jraivio/IoT-Ralli-Vempain/Hardware/Pictures/_DSC5884.JPG

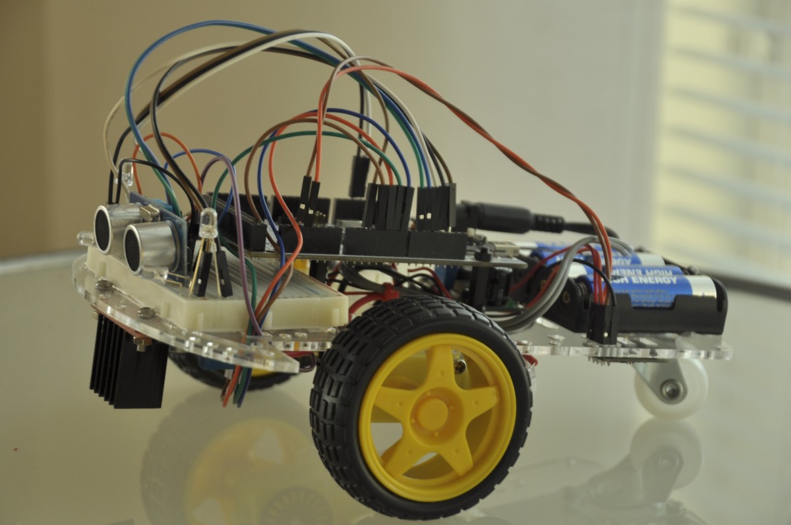
Hardware/Pictures/_DSC5884.JPG
