jraivio/IoT-Ralli-Vempain/Hardware/Pictures/Cloudyralli.png

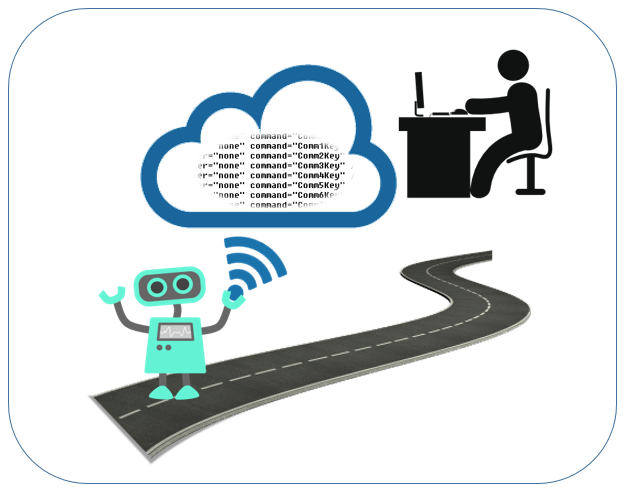
Hardware/Pictures/Cloudyralli.png
