jraivio/IoT-Ralli-Vempain/Hardware/Pictures/esp-link.png

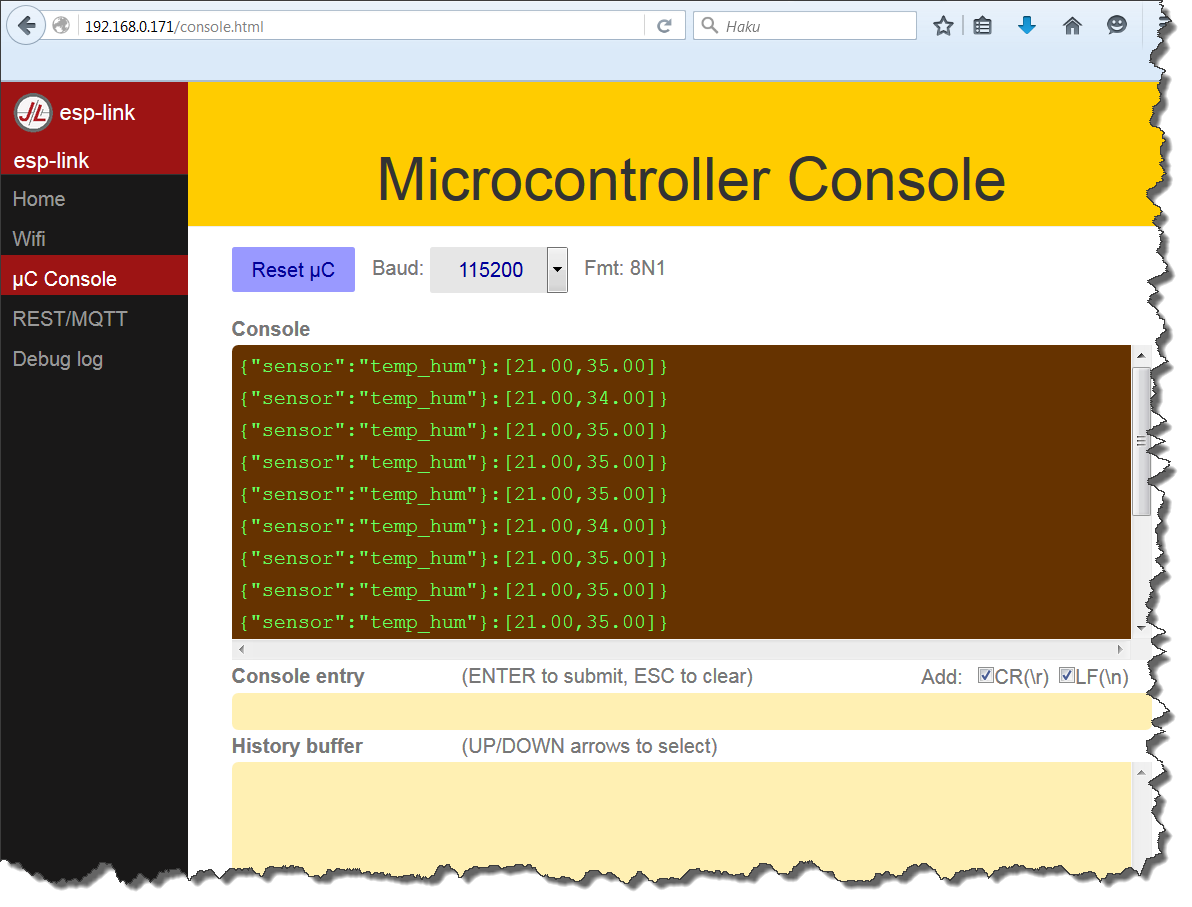
Hardware/Pictures/esp-link.png
