jraivio/IoT-Ralli-Vempain/Hardware/Pictures/Ralli-Vempain-Fritzing-wiring.png

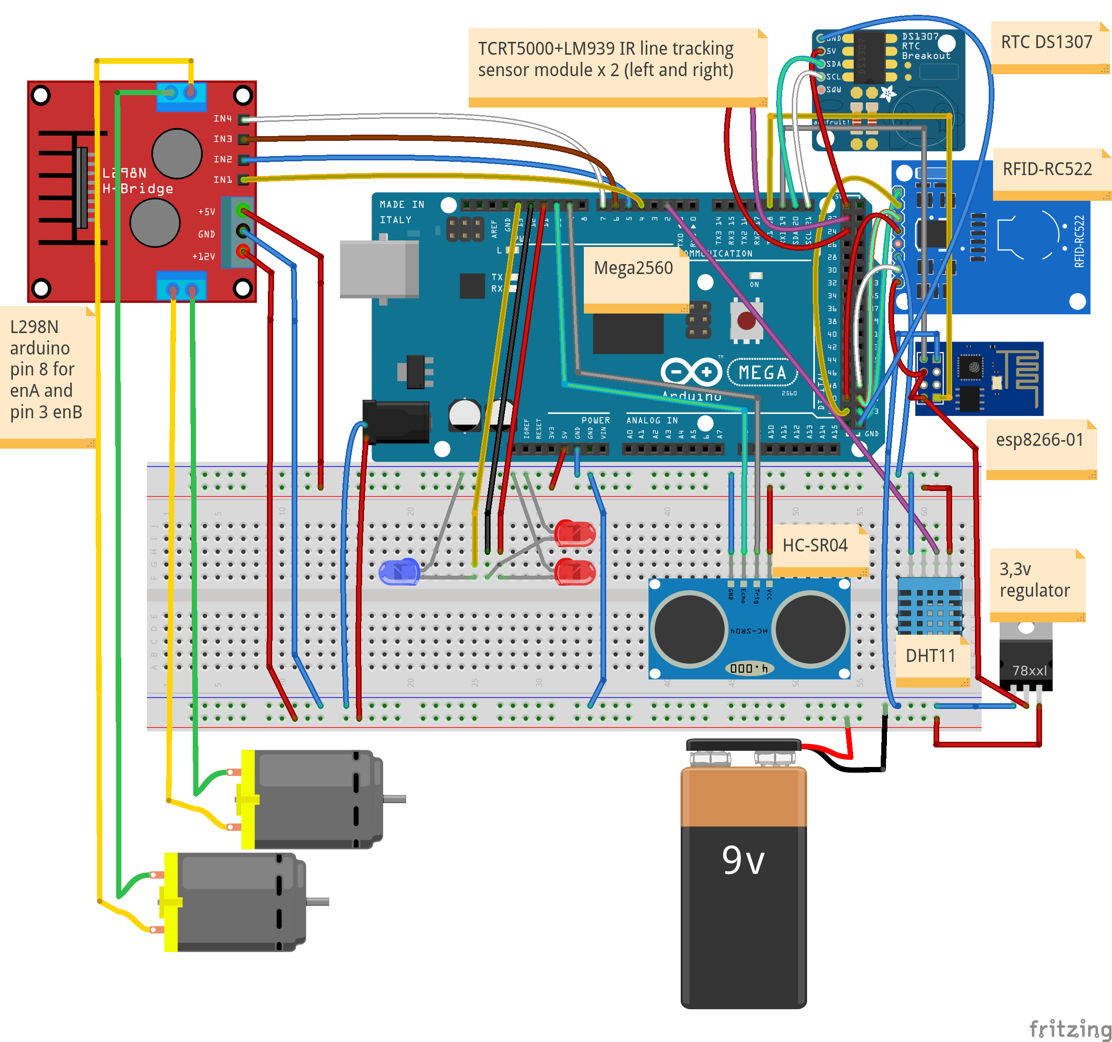
Hardware/Pictures/Ralli-Vempain-Fritzing-wiring.png
